fmck3516/midea-telemetry/schematics/schematics.kicad_sch

## KiCad design schematics/schematics.kicad_sch (2026-07-17, an earlier design)

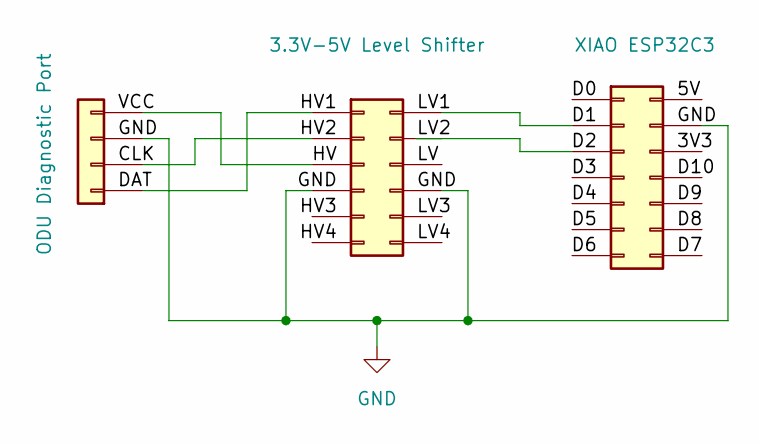
[picture p3: schematic schematics.kicad_sch]

Parts:
J1: ODU Diagnostic Port
J2: 3.3V-5V Level Shifter
J3: XIAO ESP32C3

Connections:
GND: J1.3, J2.7, J2.8, J3.13
LV2: J3.3
unnamed: J1.1, J2.1
unnamed: J1.2, J2.3
unnamed: J1.4, J2.5
unnamed: J2.2, J3.2
